TomaszWos/Guitar_AMP/VER_2/LTSPACE/Schemat przester 4  triody.asc

1k: res; 3.3k
C1: cap; 47µ
C2: cap; 22µ
C3: cap; 22n
C4: cap; 22µ
C5: cap; 22n
C6: cap; 22µ
C8: cap; 47n
C9: cap; 22n
R1: res; 1000K
R2: res; 1.5k
R3: res; 100k
R4: res; 1k
R5: res; 100k
R6: res; 220k
R7: res; 220k
R8: res; 220k
R9: res; 220k
R10: res; 22k
R11: res; 680
R12: res; 1.5k
R13: res; 100k
R14: res; 500k
R16: res; 100k
R17: res; 1000k
R18: res; 100k
R19: res; 1000k
R20: res; 22k
U1: triodeh; 12ax7
U2: triodeh; 12ax7
U3: triodeh; 12ax7
U4: triodeh; 12ax7
V1: voltage; 300
V2: voltage; SINE(0 0.1 87)
V3: voltage; SINE(0 8.92 50)
V4: voltage; SINE(0 0.05 1200)
Named nets: 0
.inc EL84.inc
.tran 10 startup uic
.four 1kHz 9 v(Out)
EL84 SE
.inc triode.inc
