TomaszWos/Guitar_AMP/VER_2/Kicad_project/wzmacniacz_v2.sch

## KiCad design VER_2/Kicad_project/wzmacniacz_v2.sch (2023-02-22)

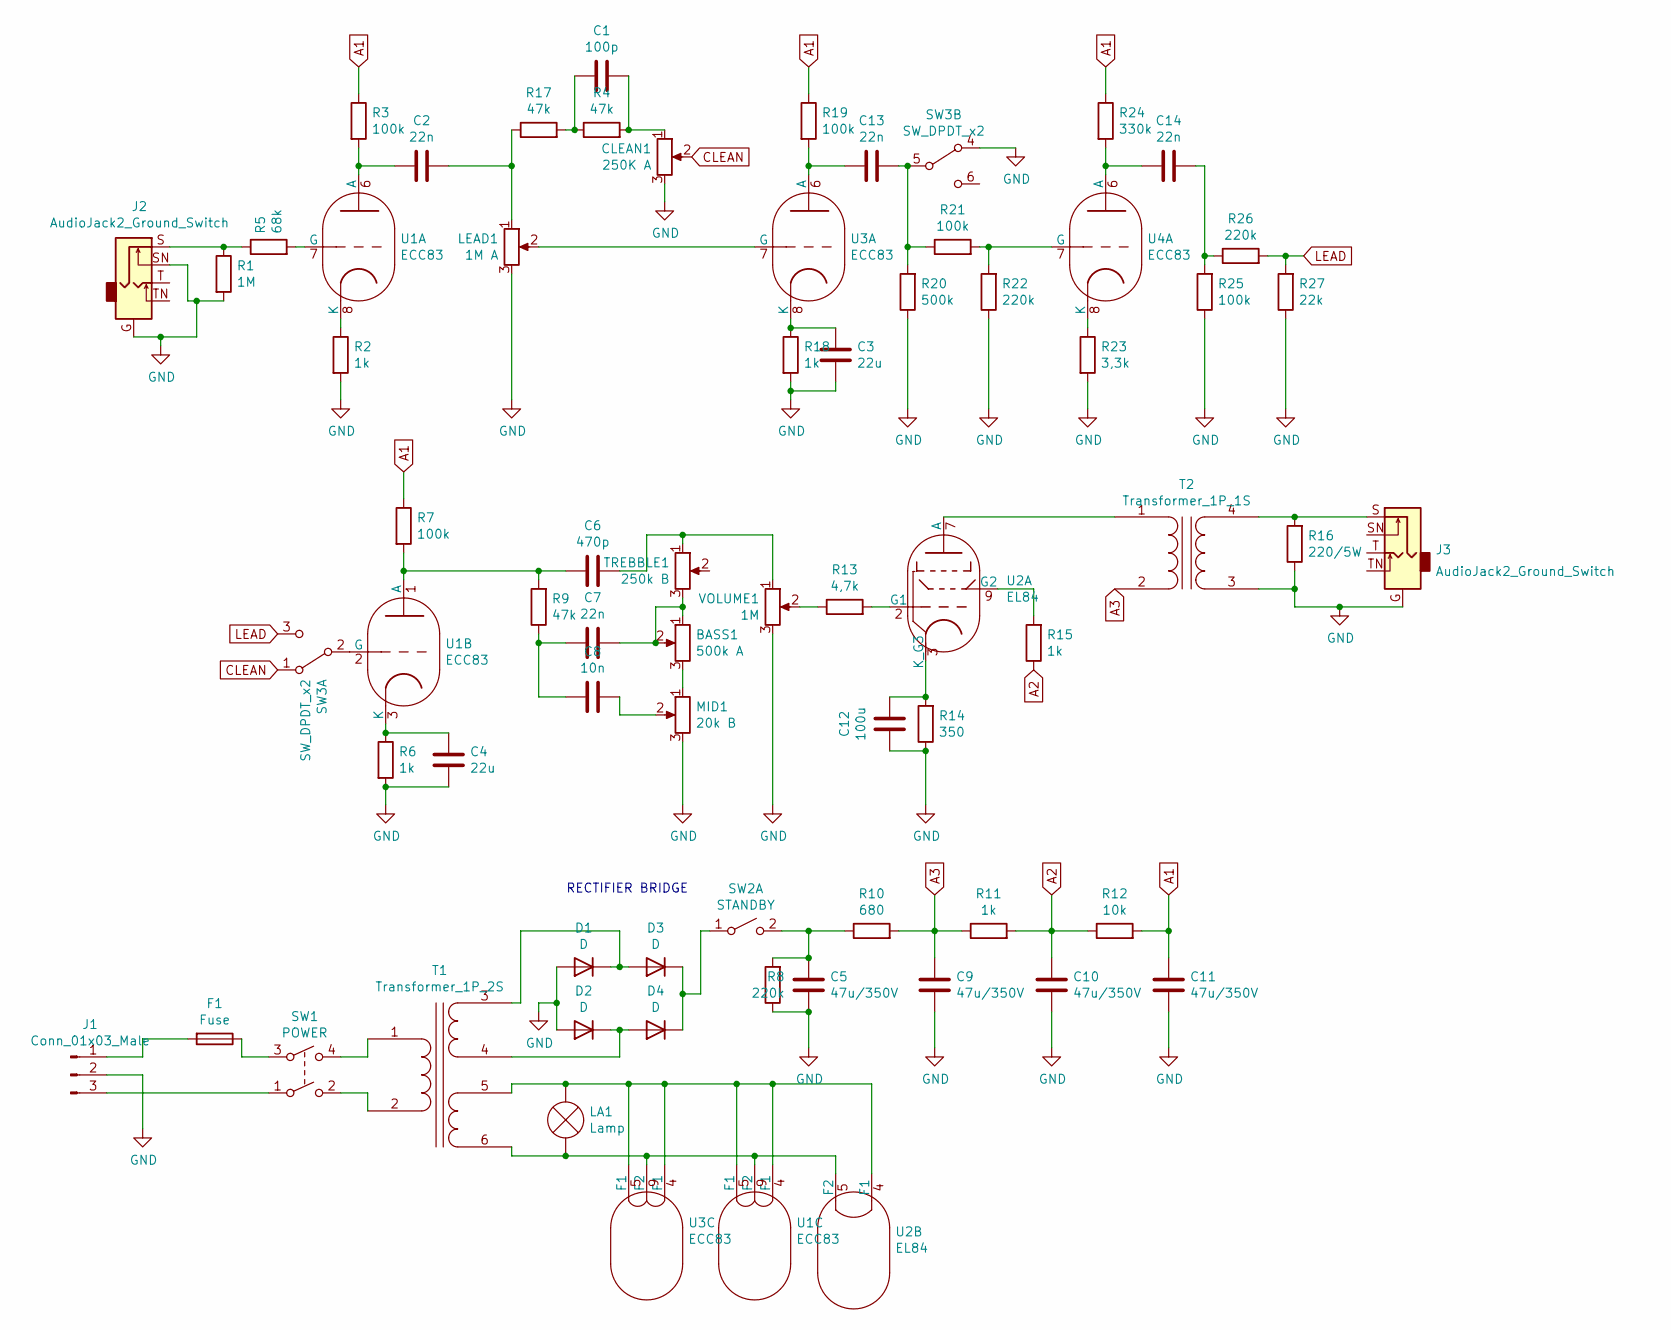
[picture p6: schematic wzmacniacz_v2.sch]

Parts:
BASS1: 500k A
C1: 100p
C2, C7, C13, C14: 22n
C3, C4: 22u
C5, C9, C10, C11: 47u/350V
C6: 470p
C8: 10n
C12: 100u
CLEAN1: 250K A
D1, D2, D3, D4: D
F1: Fuse
J1: Conn_01x03_Male
J2, J3: AudioJack2_Ground_Switch
LA1: Lamp
LEAD1: 1M A
MID1: 20k B
R1: 1M
R2, R6, R11, R15, R18: 1k
R3, R7, R19, R21, R25: 100k
R4, R9, R17: 47k
R5: 68k
R8, R22, R26: 220k
R10: 680
R12: 10k
R13: 4,7k
R14: 350
R16: 220/5W
R20: 500k
R23: 3,3k
R24: 330k
R27: 22k
SW1: POWER
SW2: STANDBY
SW3: SW_DPDT_x2
T1: Transformer_1P_2S
T2: Transformer_1P_1S
TREBBLE1: 250k B
U1, U3, U4: ECC83; Valve_Noval_P
U2: EL84; Valve_Noval_P
VOLUME1: 1M

Connections:
A1: C11.1, R3.1, R7.1, R12.2, R19.1, R24.1
A2: C10.1, R11.2, R12.1, R15.1
A3: C9.1, R10.2, R11.1, T2.2 (AB)
CLEAN: CLEAN1.2, SW3.1 (A)
GND: C3.2, C4.2, C5.2, C9.2, C10.2, C11.2, C12.1, CLEAN1.3, D1.2 (A), D2.2 (A), J1.2, J2.G, J2.SN, J3.G, LEAD1.3, MID1.3, R1.2, R2.2, R6.2, R8.1, R14.1, R16.1, R18.2, R20.1, R22.1, R23.2, R25.1, R27.1, SW3.4 (A), T2.3 (SA), VOLUME1.3
LEAD: R26.2, R27.2, SW3.3 (C)
unnamed: BASS1.1, BASS1.2, C7.2, TREBBLE1.3
unnamed: BASS1.3, MID1.1
unnamed: C1.1, R4.1, R17.2
unnamed: C1.2, CLEAN1.1, R4.2
unnamed: C2.1, R3.2, U1.6 (A)
unnamed: C2.2, LEAD1.1, R17.1
unnamed: C3.1, R18.1, U3.8 (K)
unnamed: C4.1, R6.1, U1.3 (K)
unnamed: C5.1, R8.2, R10.1, SW2.2 (B)
unnamed: C6.1, R7.2, R9.2, U1.1 (A)
unnamed: C6.2, TREBBLE1.1, VOLUME1.1
unnamed: C7.1, C8.1, R9.1
unnamed: C8.2, MID1.2
unnamed: C12.2, R14.2, U2.3 (K_G3)
unnamed: C13.1, R19.2, U3.6 (A)
unnamed: C13.2, R20.2, R21.1, SW3.5 (B)
unnamed: C14.1, R24.2, U4.6 (A)
unnamed: C14.2, R25.2, R26.1
unnamed: D1.1 (K), D3.2 (A), T1.3 (SA)
unnamed: D2.1 (K), D4.2 (A), T1.4 (SB)
unnamed: D3.1 (K), D4.1 (K), SW2.1 (A)
unnamed: F1.1, SW1.3
unnamed: F1.2, J1.1
unnamed: J1.3, SW1.1
unnamed: J2.S, R1.1, R5.1
unnamed: J3.S, R16.2, T2.4 (SB)
unnamed: LA1.1 (-), T1.6 (SD), U1.9 (F2), U2.5 (F2), U3.9 (F2)
unnamed: LA1.2 (+), T1.5 (SC), U1.4 (F1), U1.5 (F1), U2.4 (F1), U3.4 (F1), U3.5 (F1)
unnamed: LEAD1.2, U3.7 (G)
unnamed: R2.1, U1.8 (K)
unnamed: R5.2, U1.7 (G)
unnamed: R13.1, VOLUME1.2
unnamed: R13.2, U2.2 (G1)
unnamed: R15.2, U2.9 (G2)
unnamed: R21.2, R22.2, U4.7 (G)
unnamed: R23.1, U4.8 (K)
unnamed: SW1.2, T1.2 (AB)
unnamed: SW1.4, T1.1 (AA)
unnamed: SW3.2 (B), U1.2 (G)
unnamed: T2.1 (AA), U2.7 (A)

Notes on the sheet:
RECTIFIER BRIDGE
